hannu-hell/Mechanical_Thing-Addams-Family-/Index_Finger_Mid.stl

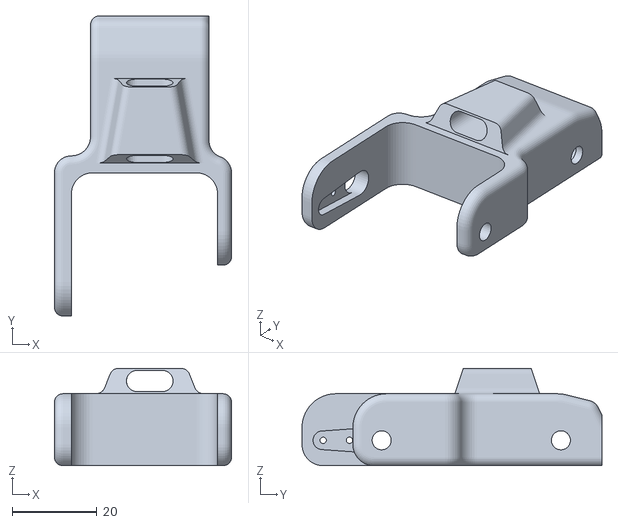
[picture p15: CAD file, 2023-10-29]
Index_Finger_Mid.stl
41.8 x 70.8 x 23.0
