hannu-hell/Mechanical_Thing-Addams-Family-/Hand_Front.stl

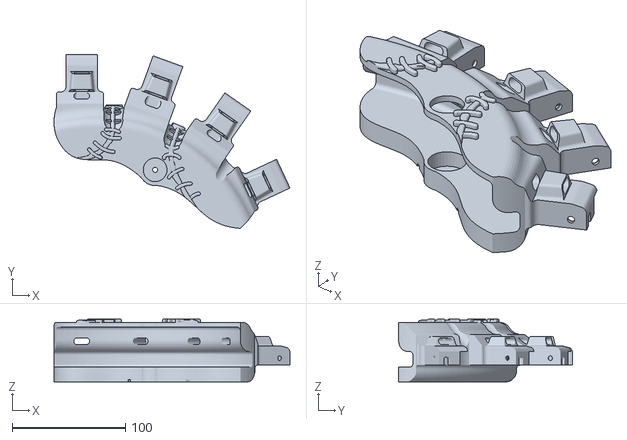
[picture p16: CAD file, 2023-10-29]
Hand_Front.stl
208.7 x 153.7 x 55.6
