hannu-hell/Mechanical_Thing-Addams-Family-/Finger_Nail.stl

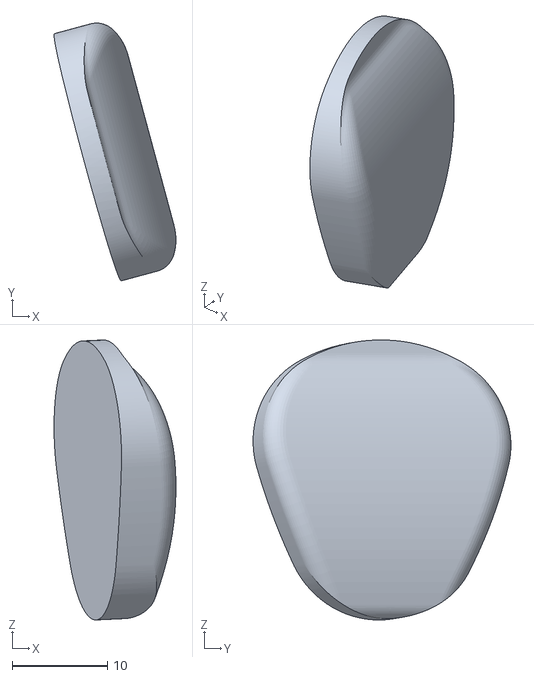
[picture p17: CAD file, 2023-10-29]
Finger_Nail.stl
12.8 x 27.1 x 29.5
