hannu-hell/Mechanical_Thing-Addams-Family-/Fingers_Horn.stl

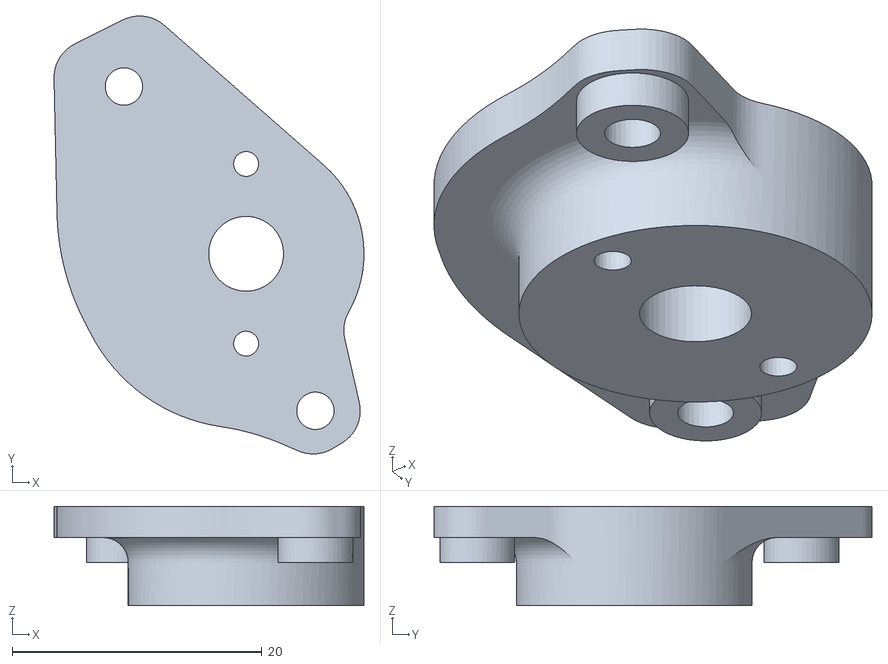
[picture p18: CAD file, 2023-10-29]
Fingers_Horn.stl
24.8 x 35.1 x 7.95
