hannu-hell/Mechanical_Thing-Addams-Family-/Cracked_Finger_Nail.stl

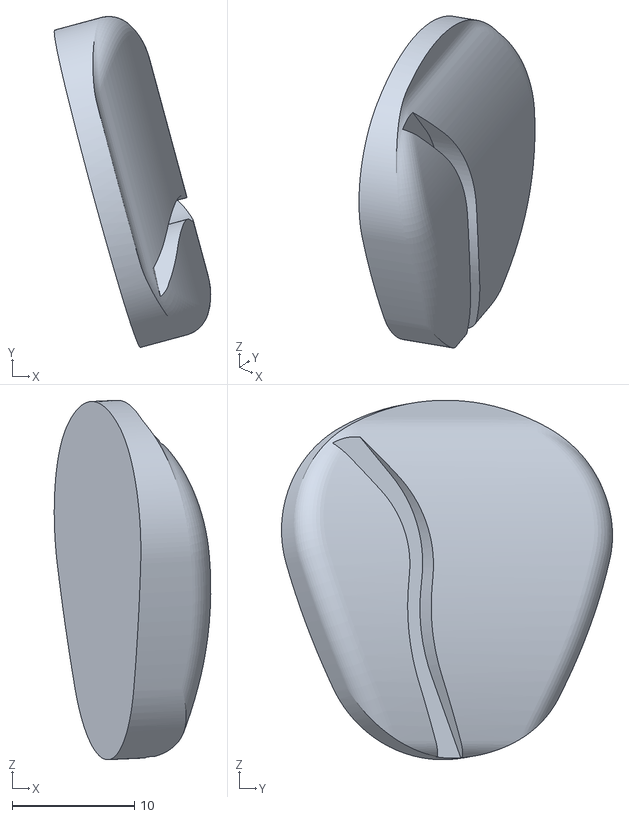
[picture p19: CAD file, 2023-10-29]
Cracked_Finger_Nail.stl
12.8 x 27.1 x 29.4
