hannu-hell/Mechanical_Thing-Addams-Family-/Wrist.stl

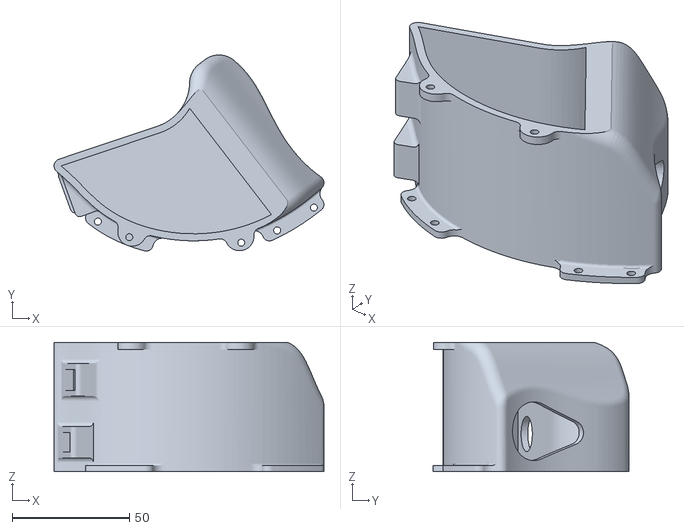
[picture p20: CAD file, 2023-10-29]
Wrist.stl
115.0 x 83.5 x 55.0
